JGuzak/mechagrid_case/models/8x16_short_light_barrier.stl

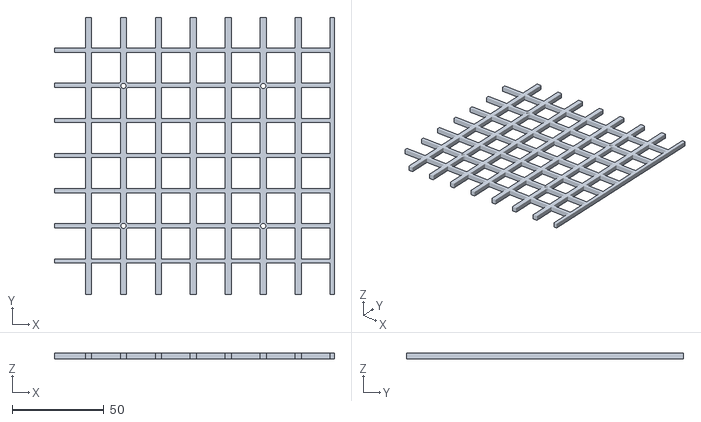
[picture p16: CAD file, 2024-07-07]
models/8x16_short_light_barrier.stl
152.2 x 150.5 x 3.50
