JGuzak/mechagrid_case/tests/test 8x16 pt1 light guard.stl

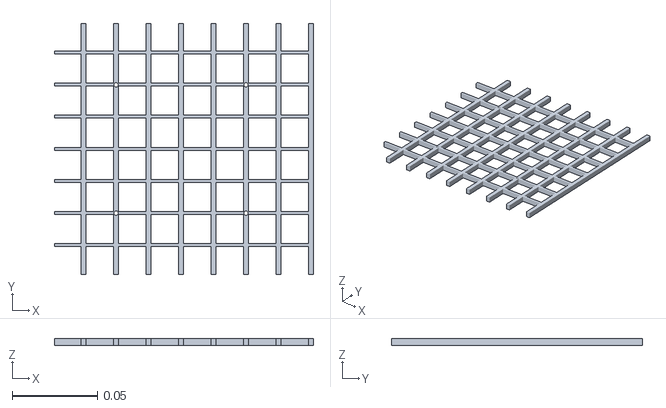
[picture p17: CAD file, 2024-06-24]
tests/test 8x16 pt1 light guard.stl
0.152 x 0.147 x 0.004
