JGuzak/mechagrid_case/models/8x16_case.stl

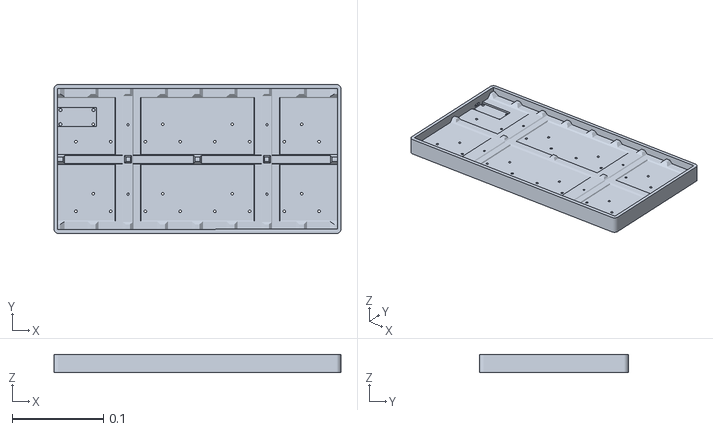
[picture p18: CAD file, 2024-07-07]
models/8x16_case.stl
0.314 x 0.163 x 0.02
