JGuzak/mechagrid_case/models/8x16_tall_light_barrier.stl

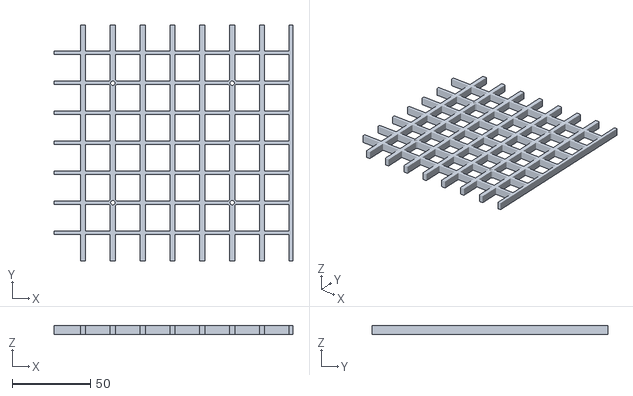
[picture p19: CAD file, 2024-07-07]
models/8x16_tall_light_barrier.stl
152.2 x 150.5 x 6.00
